weimanc/gun4ir_mods/img/IMG_20251005_001903041.jpg

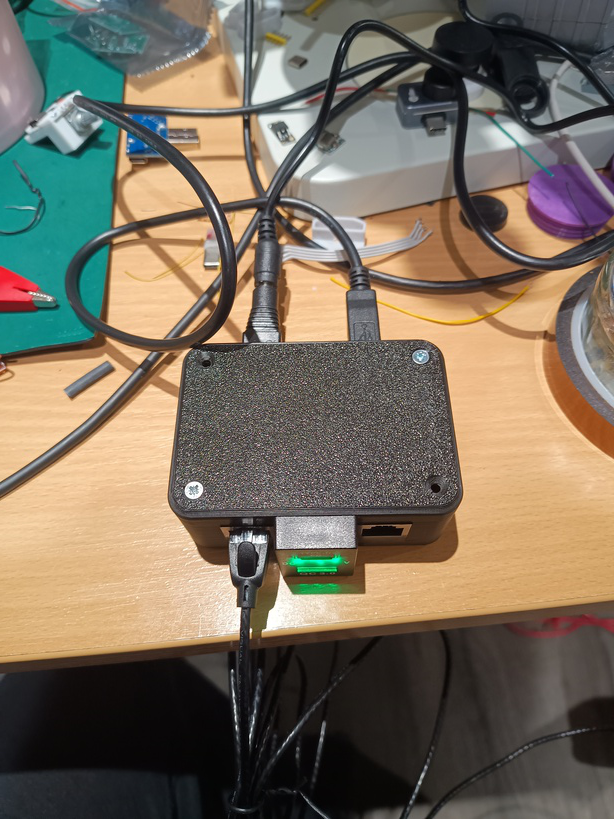
img/IMG_20251005_001903041.jpg
